paperclipsvinny/Meshtastic-Injection-Apparatus/firmware/src/StatusLED.cpp

#include "StatusLED.h"

uint8_t StatusLED::LEDPin = 0;
void StatusLED::begin(uint8_t pin){
    LEDPin = pin;
    pinMode(LEDPin, OUTPUT);
}

void StatusLED::blinkReceived(){
    #ifndef MIA_PCB
        //fast blink for visual feedback when packets recieved
        for (int i = 0; i < 3; i++){
            digitalWrite(LEDPin, HIGH);
            delay(50);
            digitalWrite(LEDPin, LOW);
            delay(50);
        }
    #endif
}
    
